neuschs/rf_transmissionline_testboard/calculations/microstrip_differential_e_field.png

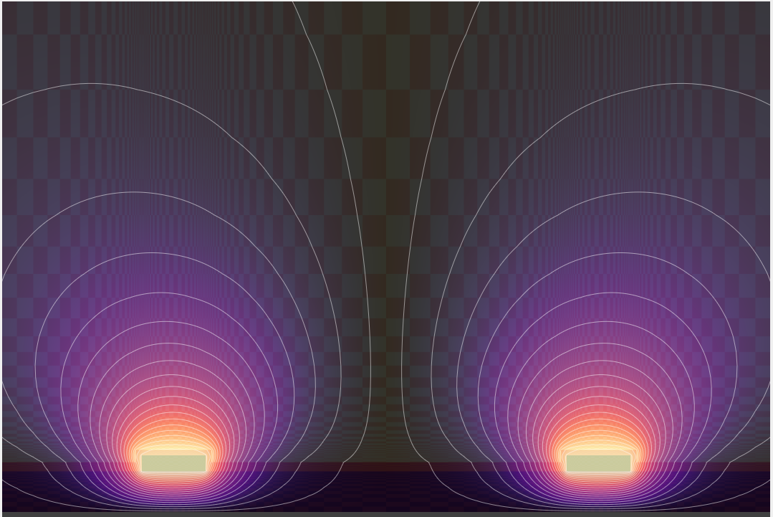
calculations/microstrip_differential_e_field.png
