neuschs/rf_transmissionline_testboard/calculations/microstrip_single_parameters.png

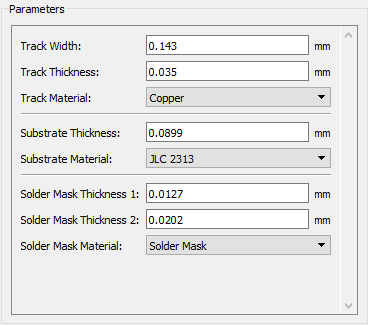
calculations/microstrip_single_parameters.png
