neuschs/rf_transmissionline_testboard/calculations/stripline_differential_e_field.png

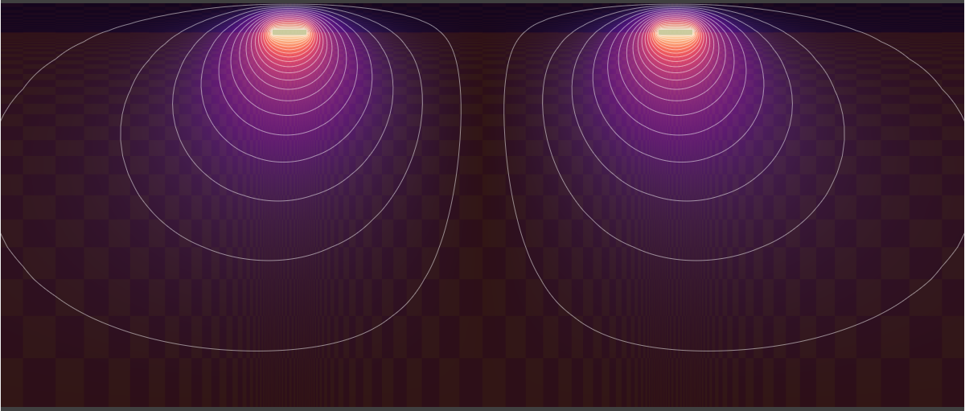
calculations/stripline_differential_e_field.png
