neuschs/rf_transmissionline_testboard/calculations/stripline_single_parameters.png

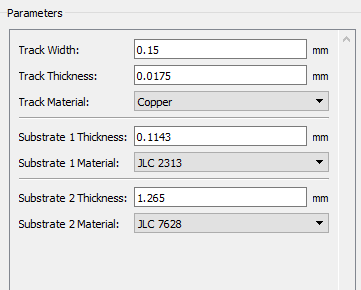
calculations/stripline_single_parameters.png
