neuschs/rf_transmissionline_testboard/calculations/coplanar_waveguide_differential_parameters.png

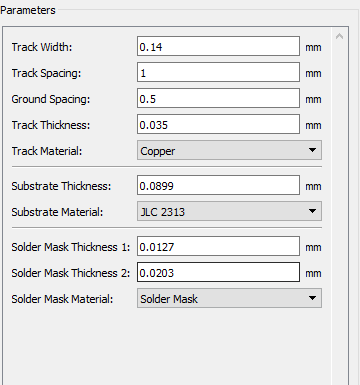
calculations/coplanar_waveguide_differential_parameters.png
