neuschs/rf_transmissionline_testboard/calculations/coplanar_waveguide_single_parameters.png

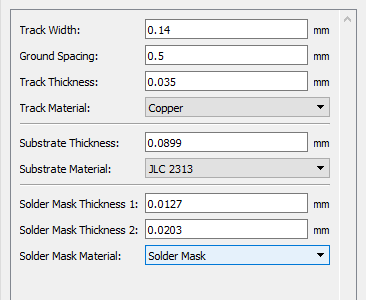
calculations/coplanar_waveguide_single_parameters.png
